koczadly/xmas-led-controller/media/photos/controller-top-down.jpg

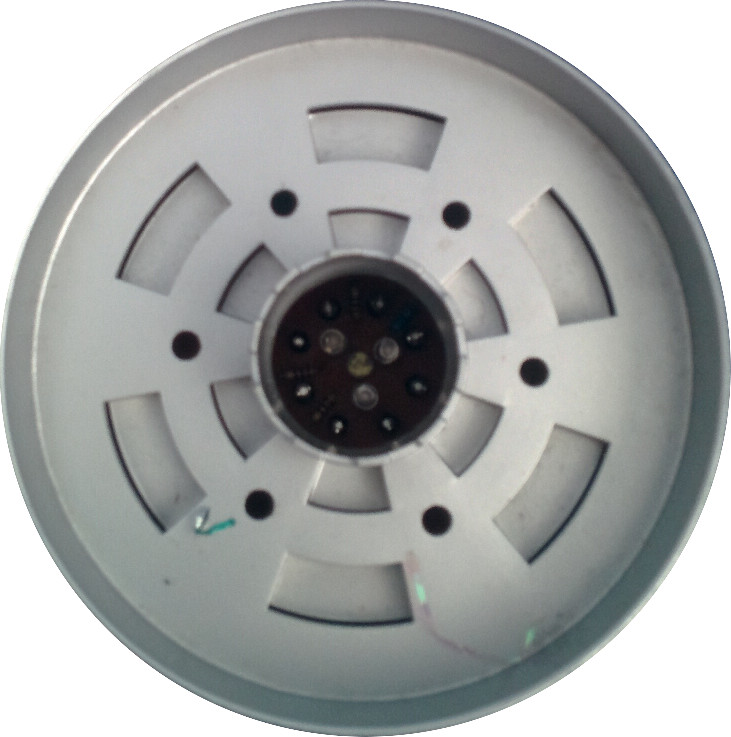
media/photos/controller-top-down.jpg
