koczadly/xmas-led-controller/media/renders/pcb-render-bottom.jpg

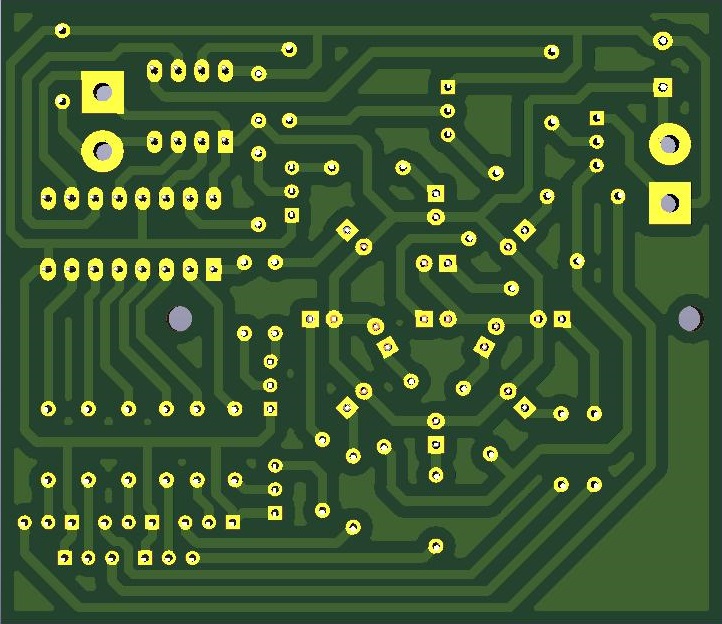
media/renders/pcb-render-bottom.jpg
