koczadly/xmas-led-controller/firmware/config.h

#include <xc.h>
#include <stdint.h>
#include <pic12f683.h>


// CONFIG
#pragma config FOSC = INTOSCIO  // Oscillator Selection bits (INTOSCIO oscillator: I/O function on RA4/OSC2/CLKOUT pin, I/O function on RA5/OSC1/CLKIN)
#pragma config WDTE = OFF       // Watchdog Timer Enable bit (WDT disabled)
#pragma config PWRTE = OFF      // Power-up Timer Enable bit (PWRT disabled)
#pragma config MCLRE = OFF      // MCLR Pin Function Select bit (MCLR pin function is digital input, MCLR internally tied to VDD)
#pragma config CP = OFF         // Code Protection bit (Program memory code protection is disabled)
#pragma config CPD = OFF        // Data Code Protection bit (Data memory code protection is disabled)
#pragma config BOREN = OFF      // Brown Out Detect (BOR disabled)
#pragma config IESO = ON        // Internal External Switchover bit (Internal External Switchover mode is enabled)
#pragma config FCMEN = ON       // Fail-Safe Clock Monitor Enabled bit (Fail-Safe Clock Monitor is enabled)

#define _XTAL_FREQ 4000000 //Frequency

//Default EEPROM
__EEPROM_DATA(0x00, 0x00, 0x00, 0x00, 0x00, 0x00, 0x00, 0x00);

#define EEPROM_ADDR_MODE 0x00 //Address for eeprom mode


#define SHIFTREG_DELAY 20 //Shift register delay period (us)


#define BTN_MODE_COOLDOWN_DELAY 5 //Button delay between presses (* 65.53ms)
#define BTN_MODE_HOLD_DELAY -3 //Button wait delay until changed (* -65.53ms)
